cdens/WxHardware/Rain Gauge/Floor.stl

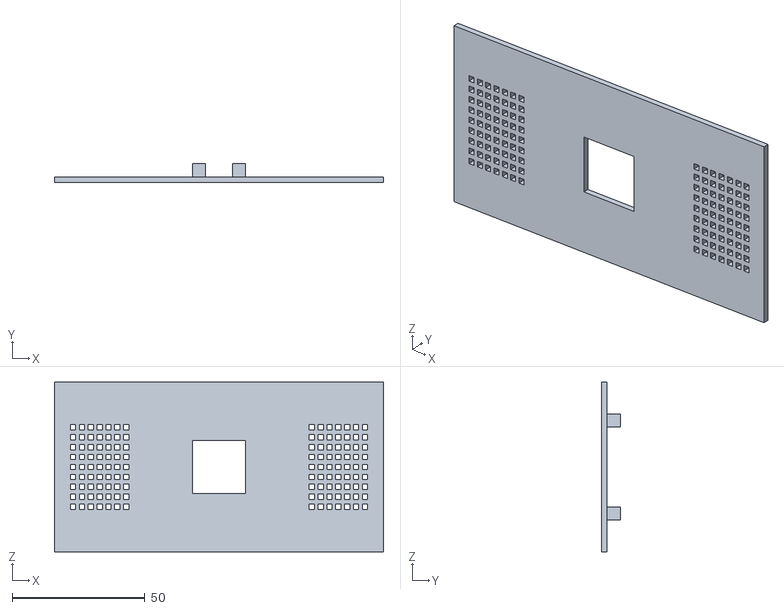
[picture p20: CAD file, 2026-10-06]
Rain Gauge/Floor.stl
124.0 x 7.00 x 64.0
