cdens/WxHardware/Wind Vane/Vane.3mf

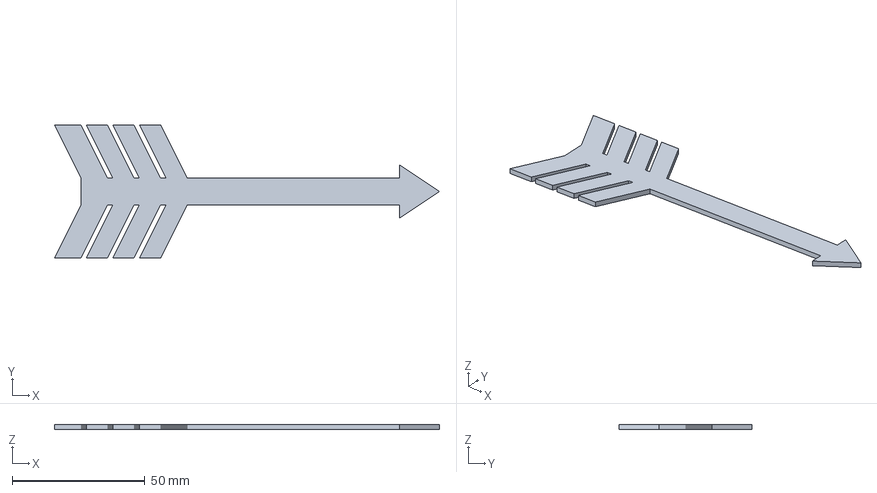
[picture p21: CAD file, 2026-10-06]
Wind Vane/Vane.3mf
145.0 x 50.0 x 2.00 mm
