cdens/WxHardware/Anemometer/Anemometer.3mf

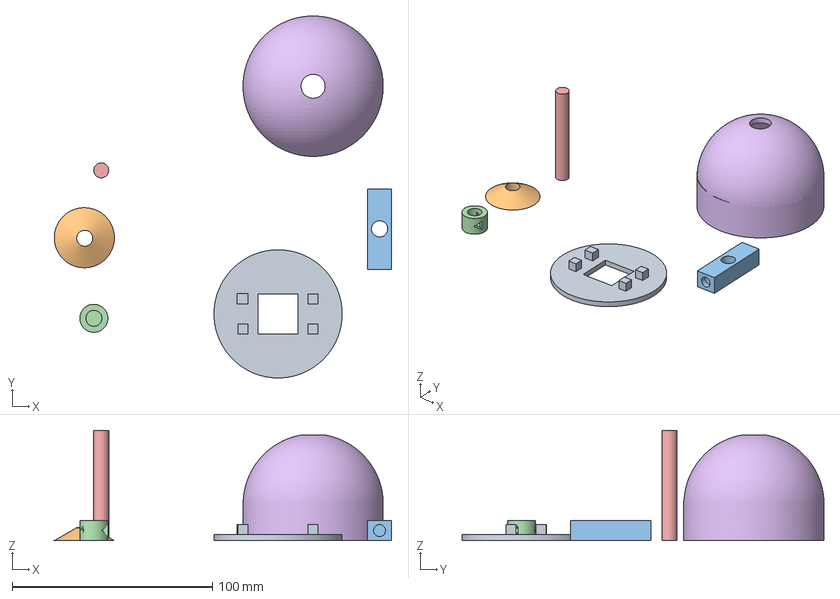
[picture p22: CAD file, 2026-10-06]
Anemometer/Anemometer.3mf
168.4 x 180.7 x 55.0 mm
Floor.stl
Rain_guard.stl
Shaft_base.stl
Shaft_joint.stl
Shaft.stl
Shell.stl
