cdens/WxHardware/Base/Hole Cover.stl

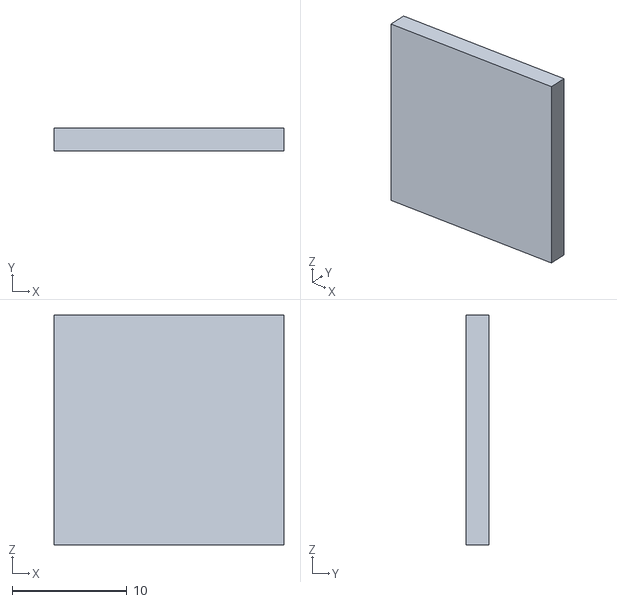
[picture p23: CAD file, 2026-10-06]
Base/Hole Cover.stl
20.0 x 2.00 x 20.0
