cdens/WxHardware/Rain Gauge/Shaft.stl

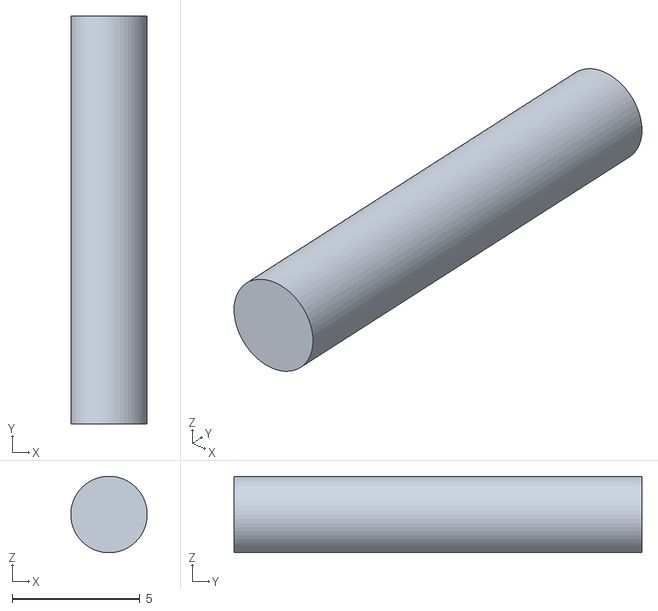
[picture p24: CAD file, 2026-10-06]
Rain Gauge/Shaft.stl
3.00 x 16.0 x 2.99
