cdens/WxHardware/Anemometer/Anemometer_Cup.3mf

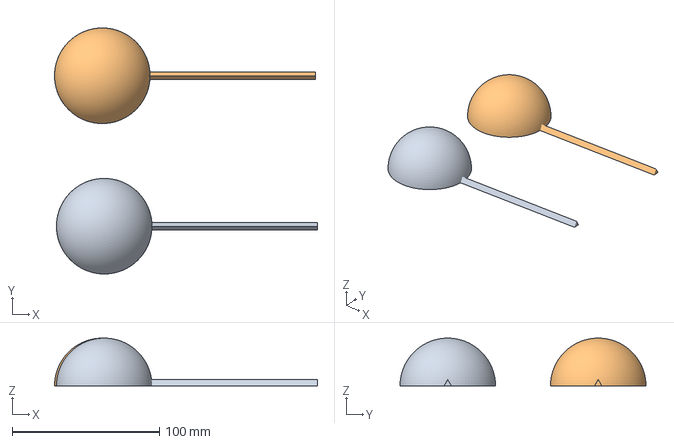
[picture p25: CAD file, 2026-10-06]
Anemometer/Anemometer_Cup.3mf
178.8 x 167.3 x 32.5 mm
Anemometer_Cup.stl x 2
