cdens/WxHardware/Base/Porthole Cover.stl

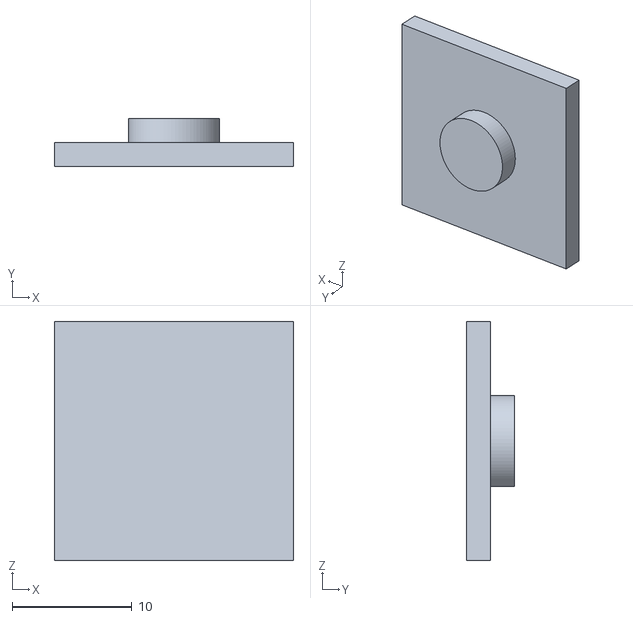
[picture p26: CAD file, 2026-10-06]
Base/Porthole Cover.stl
20.0 x 4.00 x 20.0
