cdens/WxHardware/Rain Gauge/Bucket.stl

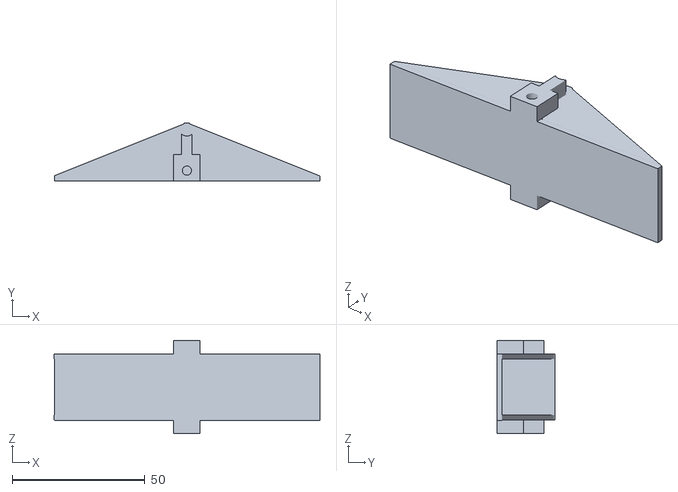
[picture p27: CAD file, 2026-10-06]
Rain Gauge/Bucket.stl
100.1 x 22.0 x 35.0
