cdens/WxHardware/Wind Vane/Wind Vane.3mf

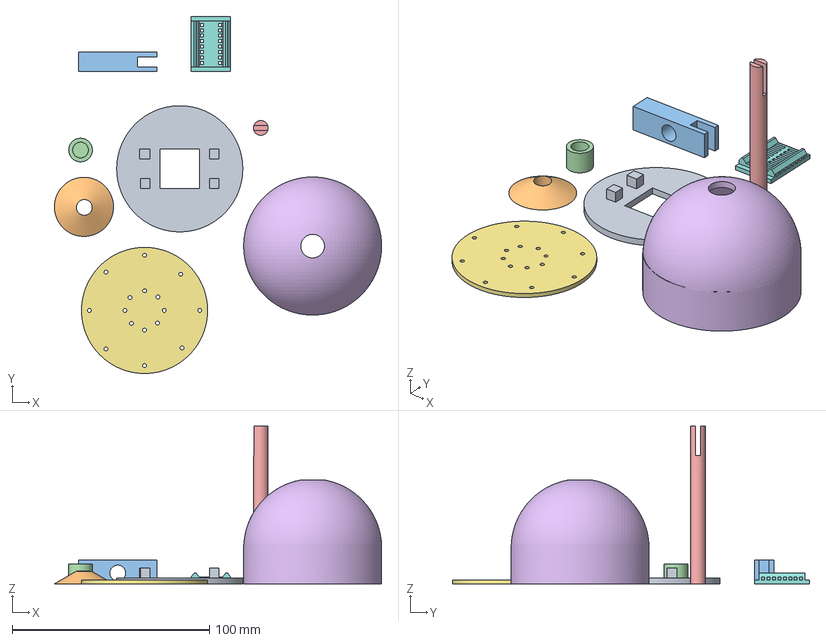
[picture p28: CAD file, 2026-10-06]
Wind Vane/Wind Vane.3mf
166.0 x 181.1 x 80.0 mm
Floor.stl
Rain_guard.stl
Shaft Base.stl
Shaft Cap.stl
Shaft.stl
Shell.stl
Internal_disk.stl
ADC_board.stl
