cdens/WxHardware/Base/Hinge shaft.stl

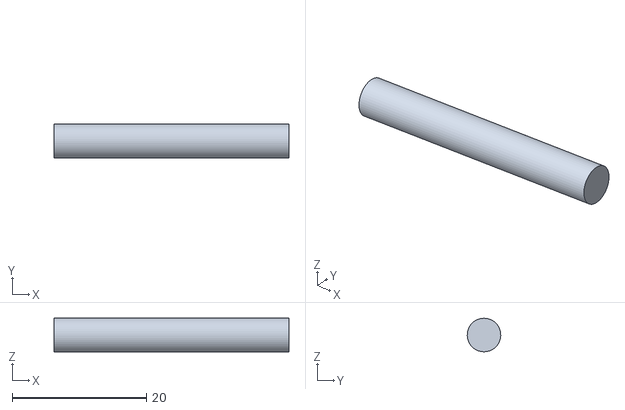
[picture p29: CAD file, 2026-10-06]
Base/Hinge shaft.stl
35.0 x 5.00 x 4.99
