cdens/WxHardware/Wind Vane/Shaft.stl

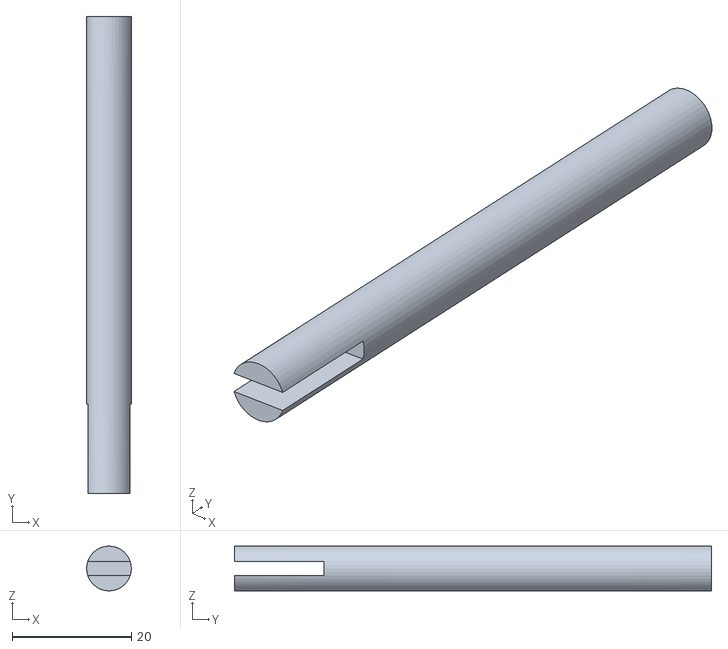
[picture p30: CAD file, 2026-10-06]
Wind Vane/Shaft.stl
7.50 x 80.0 x 7.50
