cdens/WxHardware/Base/Arm.3mf

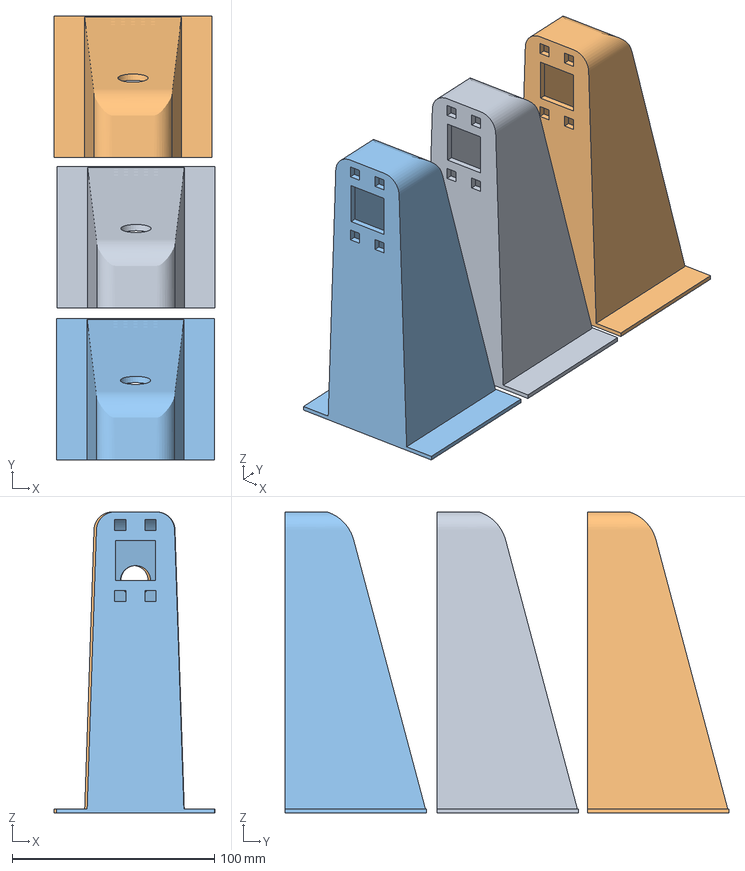
[picture p31: CAD file, 2026-10-06]
Base/Arm.3mf
79.5 x 219.7 x 149.0 mm
Arm.stl x 3
