cdens/WxHardware/Wind Vane/ADC_board.stl

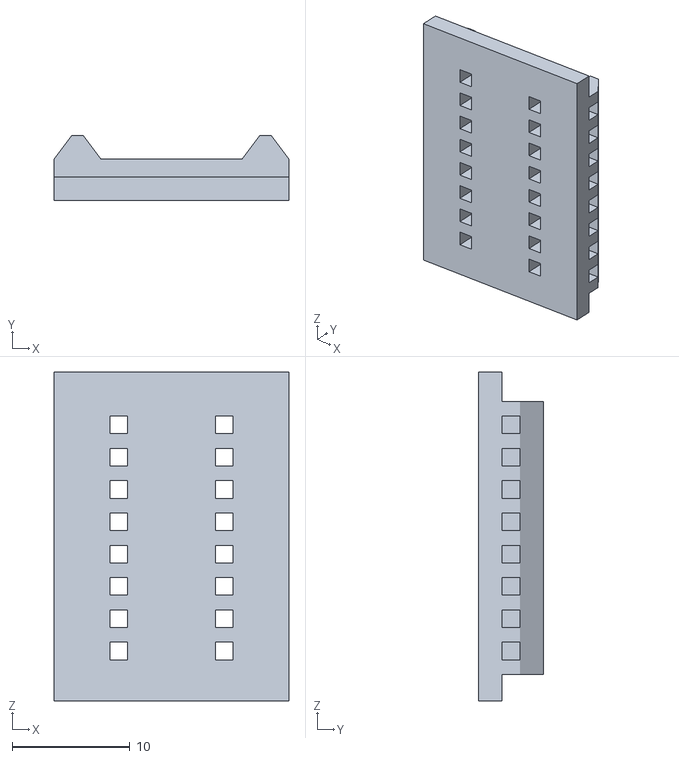
[picture p32: CAD file, 2026-10-06]
Wind Vane/ADC_board.stl
20.0 x 5.50 x 28.0
