cdens/WxHardware/Base/Housing.3mf

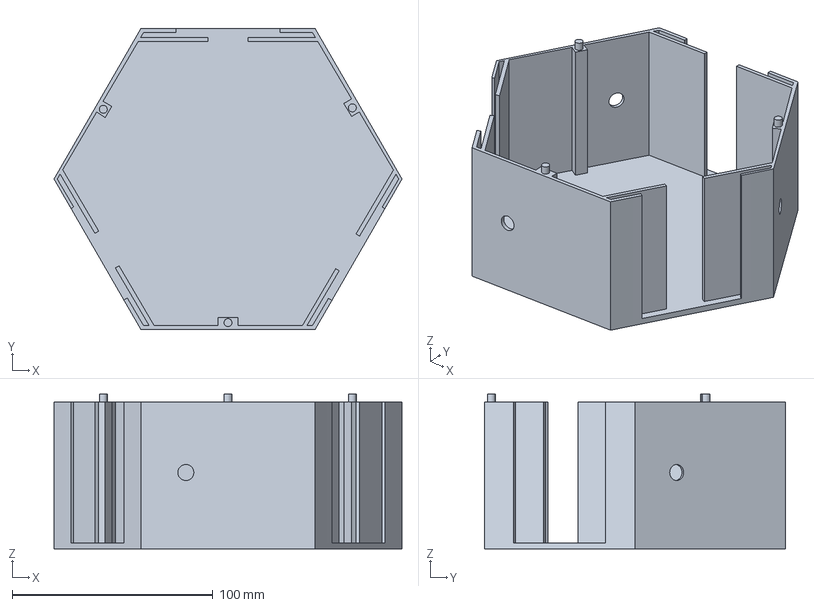
[picture p33: CAD file, 2026-10-06]
Base/Housing.3mf
173.2 x 150.0 x 77.0 mm
