cdens/WxHardware/Wind Vane/Internal_disk.stl

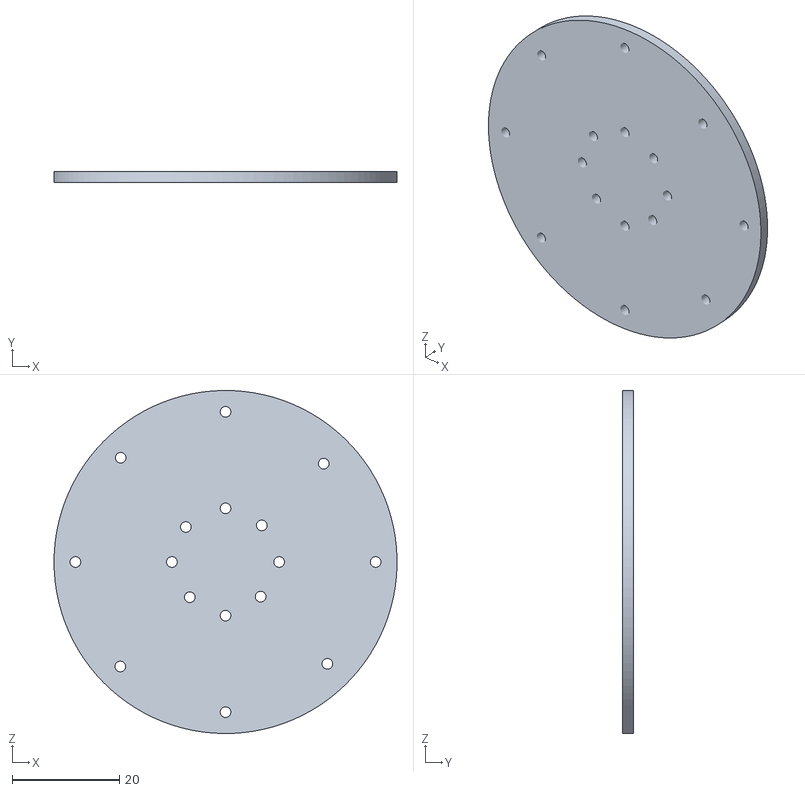
[picture p34: CAD file, 2026-10-06]
Wind Vane/Internal_disk.stl
64.0 x 2.00 x 64.0
