cdens/WxHardware/Base/Latch Upper.stl

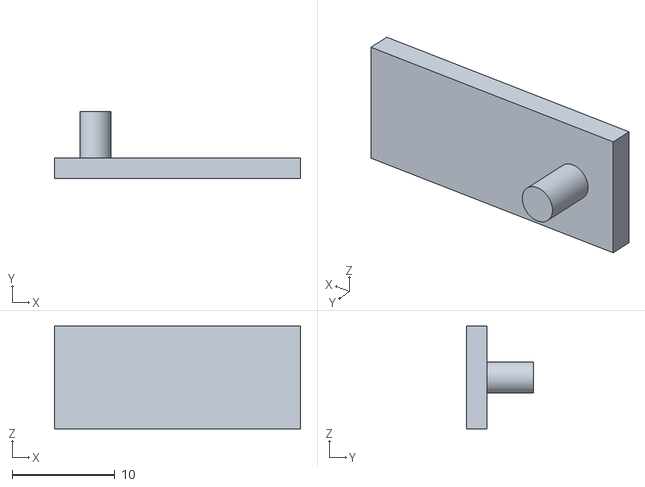
[picture p35: CAD file, 2026-10-06]
Base/Latch Upper.stl
24.0 x 6.50 x 10.0
