cdens/WxHardware/Base/Hinge Cap.stl

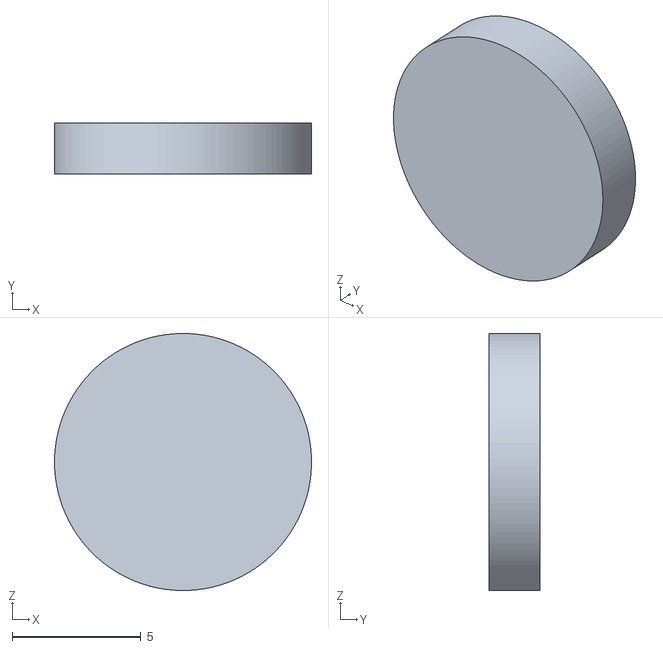
[picture p36: CAD file, 2026-10-06]
Base/Hinge Cap.stl
10.00 x 2.00 x 10.00
